xboxpro1/Switchless-Multi-ROM-for-THT-version/retroninja/applications/Switchless multi-ROM for CBM 1541/README.md

# Switchless multi-ROM for CBM 1541
Switches DOS ROM on the 1541 and other CBM IEC drives that uses 2364 ROMs. Can be used to switch ROM between CBM DOS/JiffyDOS/SpeedDOS/DolphinDOS and so on.

The switch is controlled by sending a command like *LOAD "2@RNROM",8* from the computer to switch to drive ROM image 2.

Read more in the User's guide.
