xboxpro1/Switchless-Multi-ROM-for-THT-version/retroninja/applications/Switchless multi-kernal for C64 longboard/firmware/README.md

# Firmware

The firmware directory contains source code along with some precompiled hex files for the microcontroller.

The source code is written using the Arduino environment and can be flashed directly from Arduino using an ISP programmer.
