xboxpro1/Switchless-Multi-ROM-for-THT-version/retroninja/applications/Switchless multi-ROM for CBM 1541/firmware/README.md

# Firmware

The firmware directory contains source code along with some precompiled hex files for the microcontroller.

The source code is written using the Arduino environment and can be flashed directly from Arduino using an ISP programmer.

Change log:  
1.0 - First public version for the old 1541 Multi-ROM board (rev 1, rev 1.1 & rev 2 boards) 14 May 2021  
1.1 - Updated sketch to suite the 2364 Multi-ROM board (rev 3 boards) 7 July 2022
