xboxpro1/Switchless-Multi-ROM-for-THT-version/applications/Application-Info.pdf

## CBM Switchless Multi ROM for 2364 & 27128 & 27256 ROMS

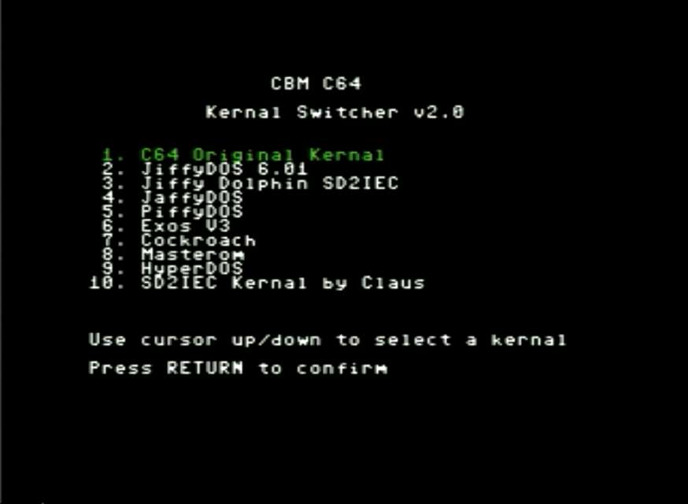
[picture p43: figure]

## Application Info

CBM Switchless Multi ROM for 2364 & 27128 & 27256 ROMS | Application Info ______________________________________________________________________

2

2

CBM Switchless Multi ROM for 2364 & 27128 & 27256 ROMS | Application Info ______________________________________________________________________

3

3

Table of Contents

CBM Switchless Multi ROM for 2364 & 27128 & 27256 ROMS | Application Info ______________________________________________________________________

4

4

Basics

Logic levels
Digital electronics rely on binary logic to store, process, and transmit data or information. Binary Logic refers to one of two states -- ON or OFF. This is commonly translated as a binary 1 or binary 0. A binary 1 is also referred to as a HIGH signal and a binary 0 is referred to as a LOW signal.
The strength of a signal is typically described by its voltage level.
How is a logic 0 (VIL) or a logic 1 (VIH) defined?
5V TTL Logic levels, maximum input LOW voltage (VIL) is 0.8 V, minimum input HIGH voltage (VIH) is 2 V.
AVR MCU Logic levels, maximum input LOW voltage (VIL) is 1.5 V,
minimum input HIGH voltage (VIH) is 3 V.
Active-Low and Active-High
When working with ICs and microcontrollers, you'll likely encounter pins that are active-low and pins that are active-high. Simply put, this just describes how the pin is activated. If it's an active-low pin, you must "pull" that pin LOW by connecting it to GND (ground). For an active high pin, you connect it to your HIGH voltage.
For example, let's say you have a flash-memory chip that has an output enable pin, OE. If you see the OE pin anywhere in the datasheet with a line over it like this, OE, then that pin is active-low. The OE pin would need to be pulled LOW in order to enable the output. If, however, the OE pin doesn't have a line over it, then it is active high, and it needs to be pulled HIGH in order to enable the output. Bit shift
A bit shift moves each digit in a number's binary representation left or right.
The left shift operator is written as "<<", the right shift operator is written as ">>". When shifting left, the most-significant bit is lost, and a 0 bit is inserted on the other end. When shifting right, the least-significant bit is lost and a 0 bit is inserted on the other end. A single left shift multiplies a number by 2, a single right shift divides a number by 2. Bit shift is faster than multiplying and dividing.
Example:
Binary | 0b0010 << 1 0b0100; 0b1010 >> 1 0b0101
Decimal | 2 << 1 4; | 10 >> 1 5

CBM Switchless Multi ROM for 2364 & 27128 & 27256 ROMS | Application Info ______________________________________________________________________

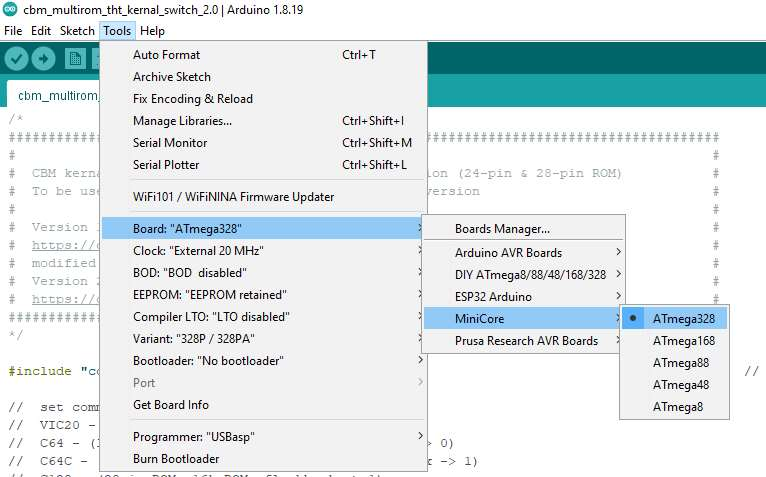
[picture p44: figure]

5

5

AVR MCU Firmware

Arduino IDE
Requirements can be found in the General-Info.pdf.
If you are new to Arduino programming, please see at: https://docs.arduino.cc/learn/starting-guide/getting-started-arduino
Please open the Arduino sketch from the /applications/arduino/firmware/v2.0/source folder with the Arduino IDE.
Then please adjust the AVR MCU you use.
Tools Board MiniCore AVR MCU (depends on what you use)

Necessary settings:
Clock External 20 MHz or 16 MHz, depends on what you use. Compiler LTO LTO disabled.
Variant depends on what you use.
Bootloader No bootloader.
If you use ISP programming you still have to set up your Programmer. All other settings can remain default.

CBM Switchless Multi ROM for 2364 & 27128 & 27256 ROMS | Application Info ______________________________________________________________________

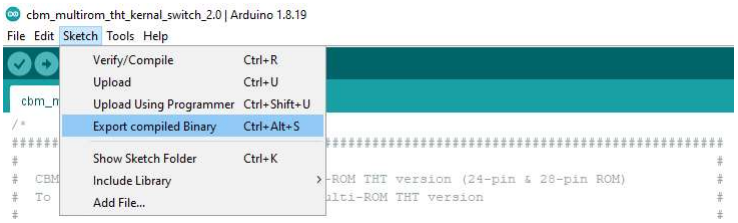
[picture p45: figure]

6

6

AVR MCU Firmware

Defining the Sketch
The sketch contains many comments and is self-explanatory. Please define the CBM Computer for which the firmware should be.

If you don't want the LED to blink, you can disable the LED by commenting it out.

These are all settings, nothing more needs to be done. Compiling
Now please compile the firmware and load it onto your MCU.
If you are programming via ISP, click Sketch Upload Using Programmer.
For an Universal Programmer or AVRDUDESS click Sketch Export compiled Binary.

CBM Switchless Multi ROM for 2364 & 27128 & 27256 ROMS | Application Info ______________________________________________________________________

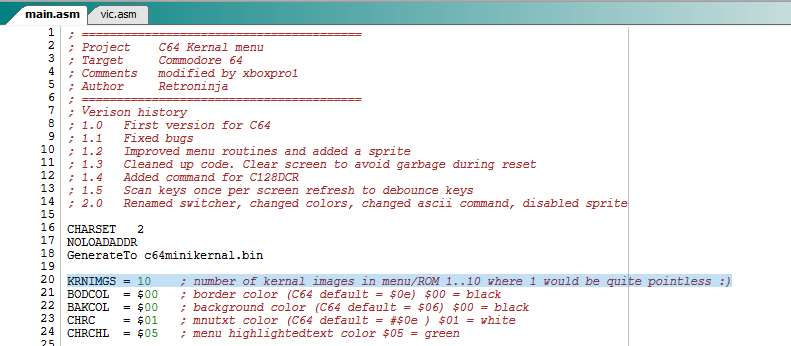
[picture p46: figure]
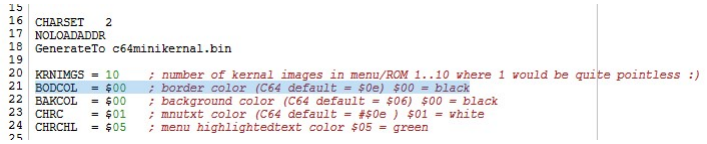
[picture p47: figure]

7

7

Mini Kernal

CBM prg Studio
Requirements can be found in the General-Info.pdf.
CBM prg Studio tutorials can be found here: https://oldskoolcoder.co.uk/cbm-prg-studio-tutorials/
Each CBM Computer has its own mini Kernal source file.
Folder /applications/cbm-prog-studio/mini-kernal/v2.0/ | /source.
Please open the project file with the ending “.cbmprj” of the desired CBM Computer using the CBM prg Studio program.
Now you can design your personal Switchless mini Kernal menu in the main.asm file. Such as the number of Kernal ROM image entries in the Switchless mini Kernal menu.

Also the frame, background and text colors.

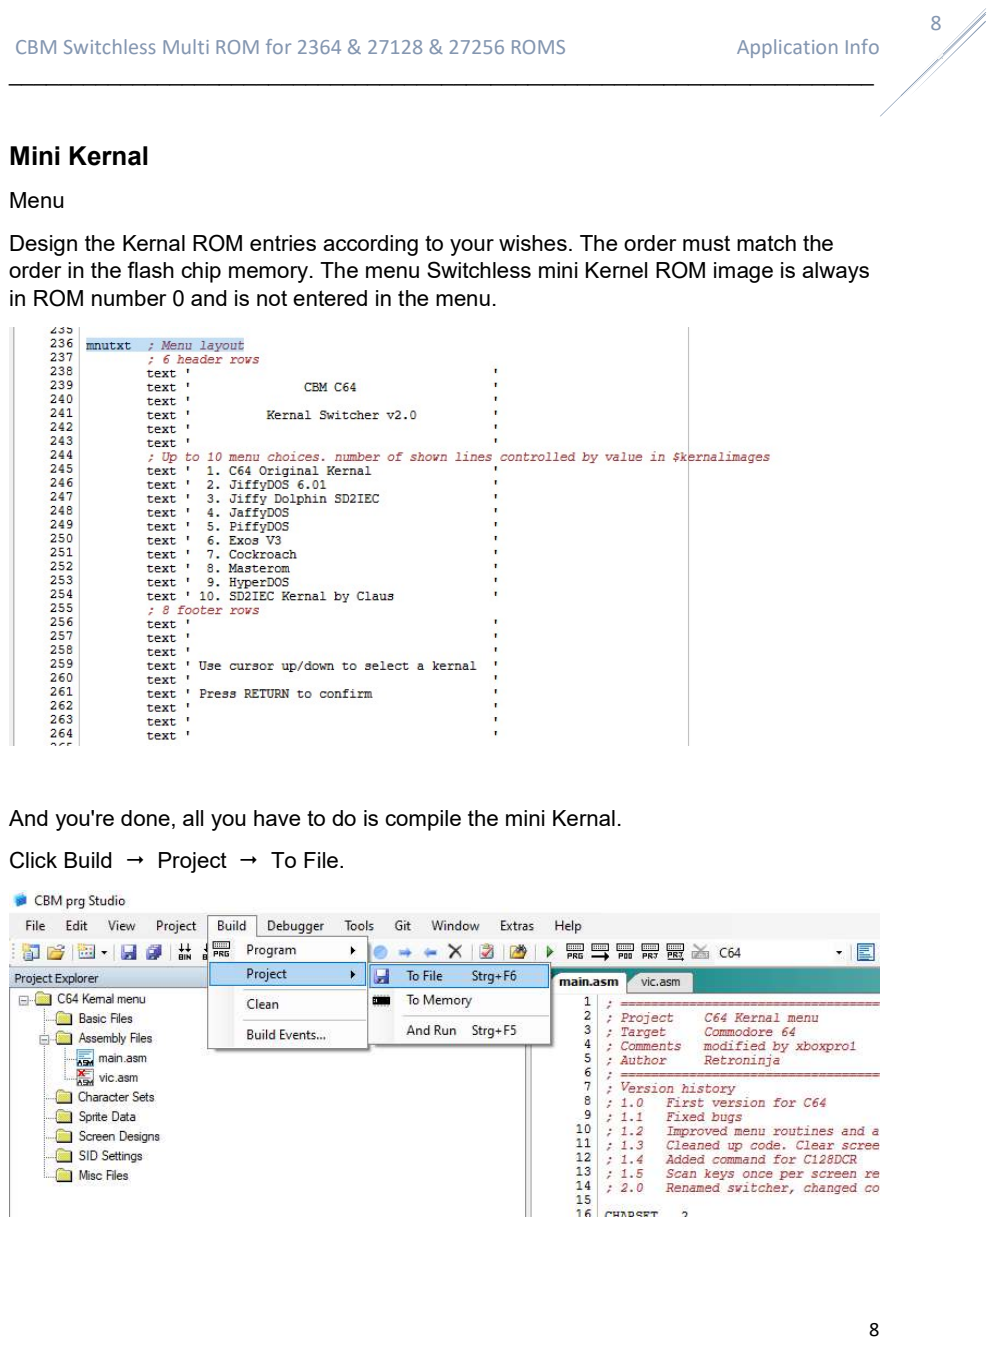
[picture p48: page 8]

CBM Switchless Multi ROM for 2364 & 27128 & 27256 ROMS | Application Info ______________________________________________________________________

8

8

Mini Kernal

Menu
Design the Kernal ROM entries according to your wishes. The order must match the order in the flash chip memory. The menu Switchless mini Kernel ROM image is always in ROM number 0 and is not entered in the menu.

And you're done, all you have to do is compile the mini Kernal. Click Build Project To File.

CBM Switchless Multi ROM for 2364 & 27128 & 27256 ROMS | Application Info ______________________________________________________________________

9

9

Flash-memory Chip

The Excel sheet in the tools folder, macros are harmless but not necessary, show you the memory allocation for the 8k, 16k and 32k ROM modes.
The mode depends on the CBM Mainboard / Kernal ROM chip.
VIC20 and C64 (longboard) normally has an 8k Kernal ROM.
C64C (shortboard) normally has an 16k Kernal ROM. Basic and Kernal in one ROM. C128 has two 16k ROM chips, one for the C128 mode and one for the C64C mode. C128DCR has a 32k Kernal ROM.
The memory area is divided into three banks. Bank 0 8k ROM, Bank 1 16k ROM and Bank 2 32k ROM. The memory banks are divided into ROM numbers for each Kernal. The Switchless mini Kernel ROM image is always in ROM number 0.
For Bank 1 and Bank 2, the kernel is selected in the firmware by bit shifting the ROM number to the left with the bank number.
Bank 0 VIC20, C64

Bank 1 C64C

Bank 1 C128

Bank 2 C128DCR

For more information, please see RetroNynjah's user guides in the retroninja folder.

Kernal | Mini Kernal 8k | CBM Kernal 8k | JiffyDOS 8k | JaffyDOS 8k | Exos V3 8k | HyperDOS 8k
Size | 8k | 8k | 8k | 8k | 8k | 8k
ROM number | 0 | 1 | 2 | 3 | 4 | 5
Kernal | C64 Basic 8k | Mini Kernal 8k | C64 Basic 8k | CBM Kernal 8k | C64 Basic 8k | JiffyDOS 8k
Size | 16k | | 16k | | 16k
ROM number | 0 | | 2 | | 4
Kernal | C128 Mini Kernal 16k | C128 CBM Kernal 16k | C128 JiffyDOS US 16k | C128 JiffyDOS DK 16k
Size | 16k | 16k | 16k | 16k
ROM number | 0 | 2 | 4 | 6
Kernal | C64 Basic 8k | C64 Mini-Kernal 8k | C128 Mini-Kernal 16k | C64 Basic 8k | C64 CBM-Kernal 8k | C128 CBM-Kernal 16k
Size | 32k | | | 32k
ROM number | 0 4

CBM Switchless Multi ROM for 2364 & 27128 & 27256 ROMS | Application Info ______________________________________________________________________

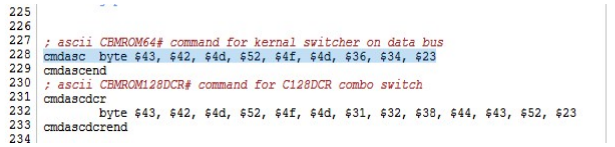
[picture p49: figure]
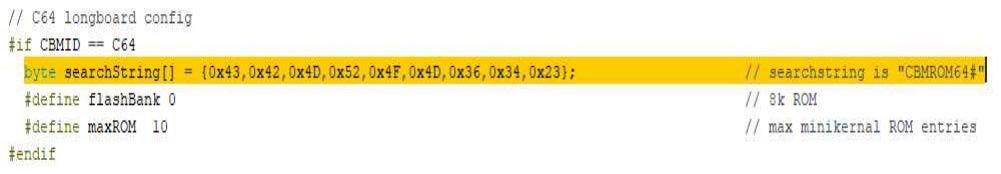
[picture p50: figure]

10

10

Change Source

You can of course change the source codes according to your requirements.
For example, changing the predefined command string of ”magic bytes”.
If you change the predefined command string in the Switchless mini Kernel source code, it also needs to be changed in the AVR MCU source code.

There are two PDF files in the tools folder with the ASCII and color codes. The codes are decimal and they must be converted to hexadecimal. Programming

Flash memory
To program the flash memory chip you need a USB universal programmer such as the TL866II Plus. A PLCC32-DIP32 adapter is also required.
Tutorial: https://projectiot123.com/2023/05/16/how-to-use-the-tl866ii-plus-programmer/ The easiest way is to first create a flash file with all the Kernal ROM images you want. Copy all the Kernal ROM images into a folder including a basic ROM.
For example, for an 8K ROM flash file, use the Windows command:
copy /b c64minikernal.bin+c64kernal.bin+jiffydos.bin+exos3.bin+sd2iec.bin flash.bin For example, for an 16K ROM flash file, use the Windows command:

copy /b basic.bin+minikernal.bin+basic.bin+c64kernal.bin+basic.bin+exos3.bin flash.bin For example, for an 32K ROM flash file, use the Windows command:
copy /b c64basic.bin+c64minikernal.bin+c128minikernal.bin+ c64basic.bin+c64kernal.bin+c128kernal.bin flash.bin

This is just an example, of course all of your desired Kernal images must be attached. Use the Universal programmer software to write the flash image to the flash chip.

CBM Switchless Multi ROM for 2364 & 27128 & 27256 ROMS | Application Info ______________________________________________________________________

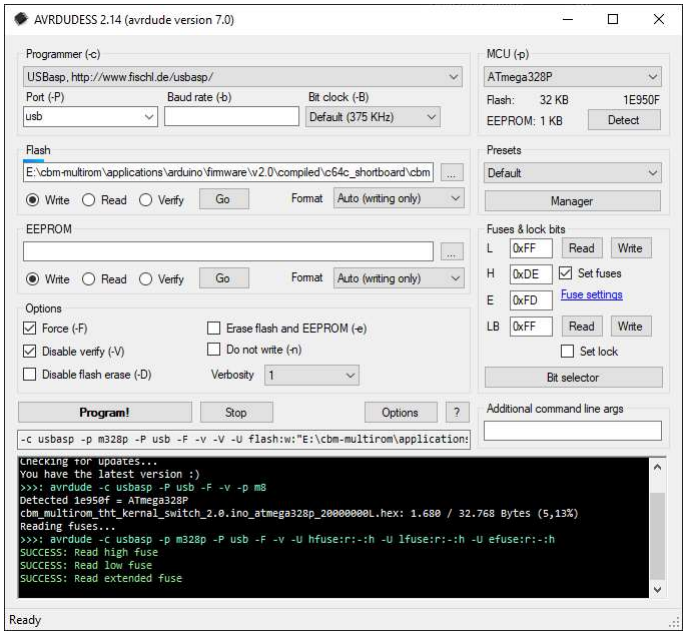
[picture p51: figure]

11

11

Programming

AVR MCU
You can also flash the AVR MCU with the USB universal programmer. Or you can use an ISP programmer to flash the MCU.
If you use an ISP programmer, I recommend the program AVRDUDESS. Requirements can be found in the General-Info.pdf.
With AVRDUDESS you can easily read and write the MCU fuses. There is also a fuse Bit selector and a link to a website where you can get the correct settings for the fuses.

Recommended fuse settings are in the fuses.txt file in the tools folder.

CBM Switchless Multi ROM for 2364 & 27128 & 27256 ROMS | Application Info ______________________________________________________________________

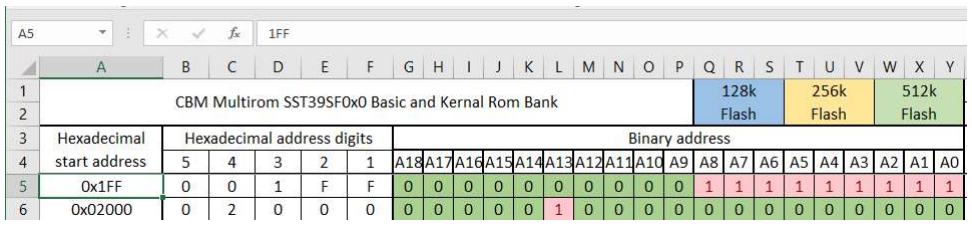
[picture p52: figure]

12

12

Tools

Excel sheet
In the Excel sheet addresscalc.xlsm in the tools folder you can enter any addresses from 0 to 7FFFF at cell A5.
Please do not write 0x at the beginning, Excel will do that itself.
This causes the address bits A0 to A18 to be set according to the respective address.

The Excel sheet has a sheet protection so that no formula can be deleted accidentally. The code to remove the sheet protection is 1234.
CircuitVerse
On CircuitVerse you can create simulations with digital components. https://circuitverse.org/simulator You can use the MultiromOE.cv file in the tools folder to simulate IC5 the single “AND”

Gate for experimental testing.
To use it click: Project Import file

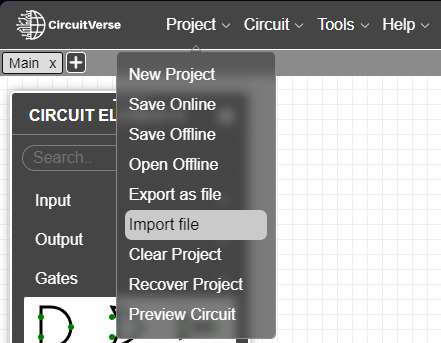
[picture p53: figure]
