xboxpro1/Switchless-Multi-ROM-for-THT-version/tools/cbm-color-codes.pdf

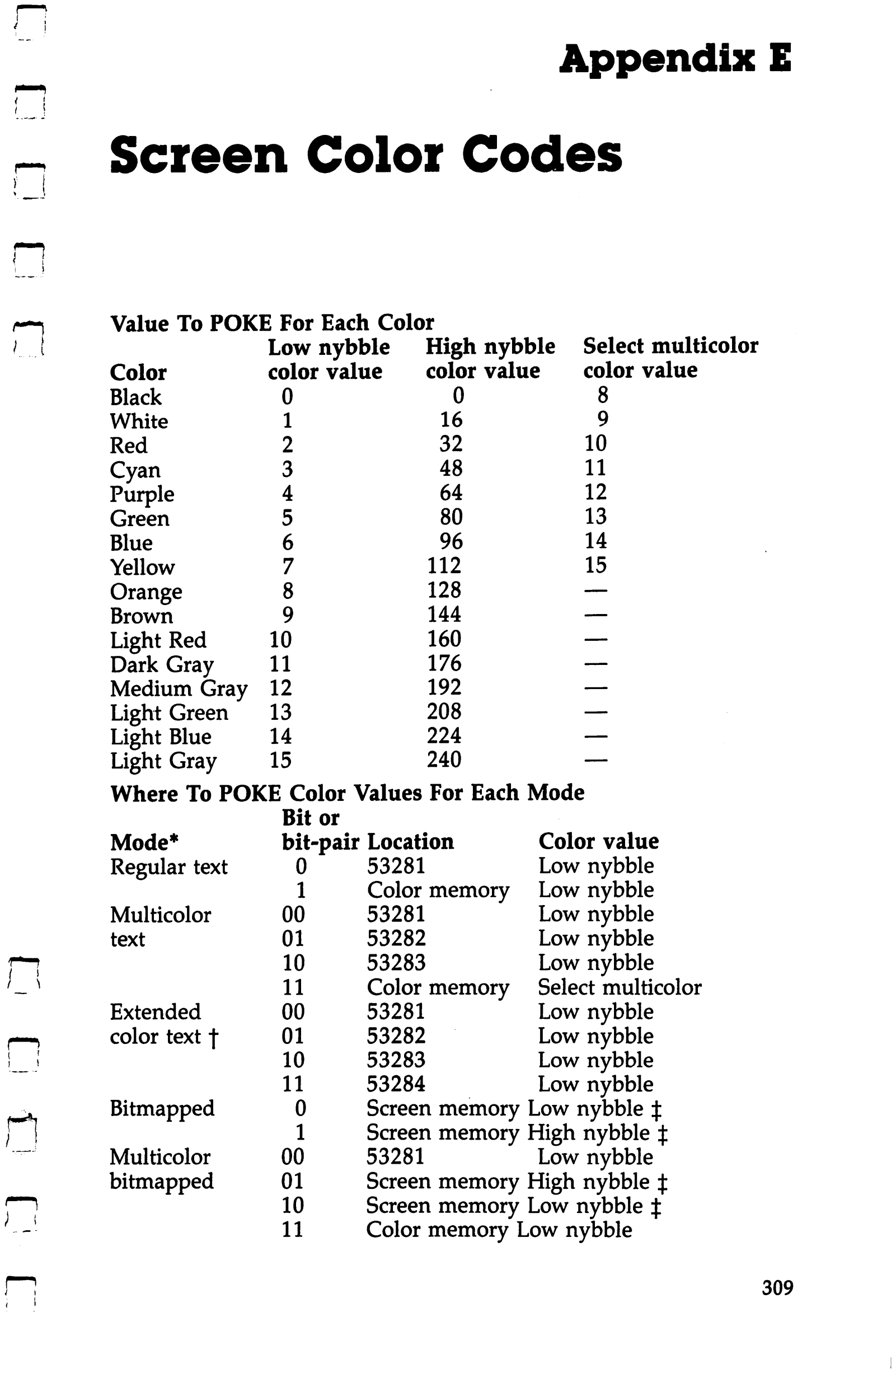
[picture p54: figure]
