xboxpro1/Switchless-Multi-ROM-for-THT-version/images/cbm-multirom-back-transparent.png

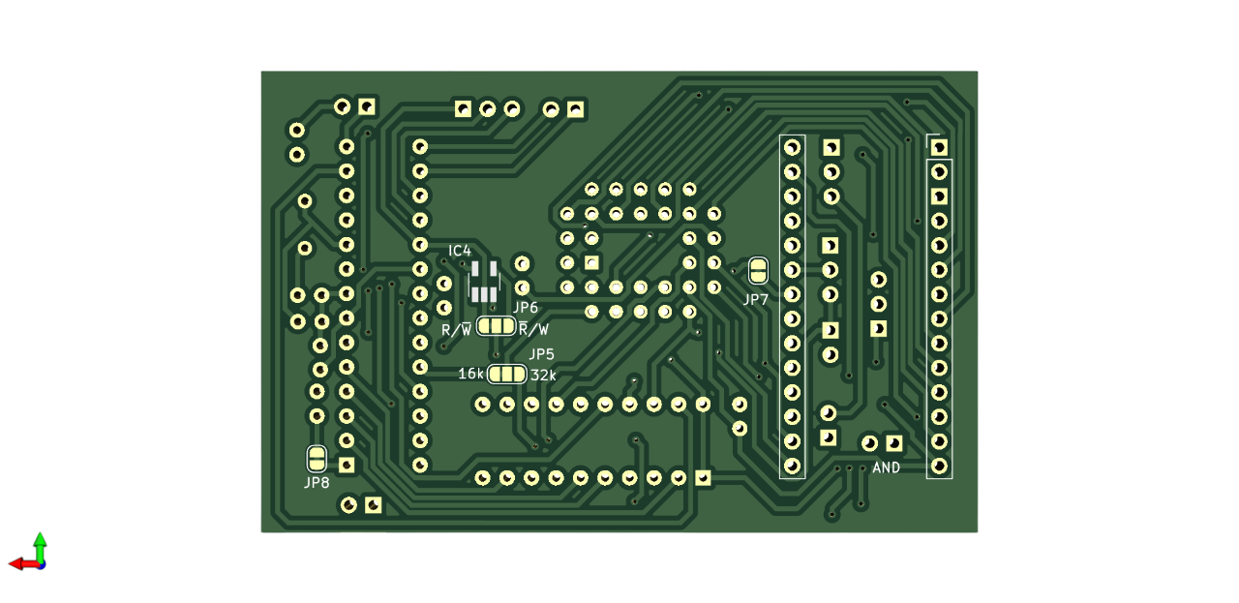
images/cbm-multirom-back-transparent.png
