xboxpro1/Switchless-Multi-ROM-for-THT-version/images/cbm-multirom-front-transparent.png

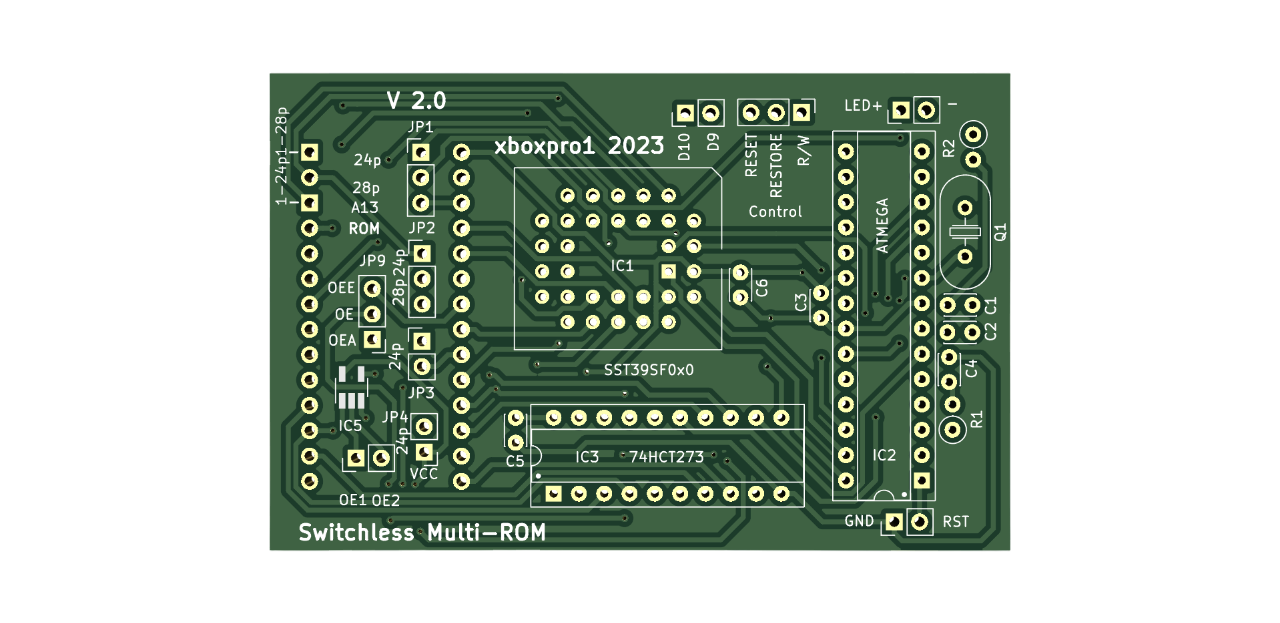
images/cbm-multirom-front-transparent.png
