xboxpro1/Switchless-Multi-ROM-for-THT-version/images/cbm-multirom-smd-pcb-front.png

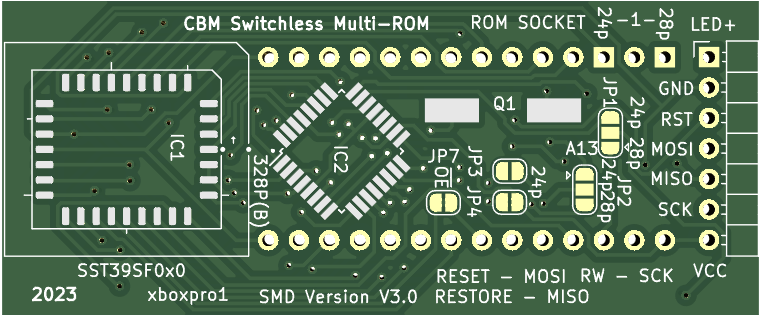
images/cbm-multirom-smd-pcb-front.png
