xboxpro1/Switchless-Multi-ROM-for-THT-version/pictures/keyboard-holder.jpg

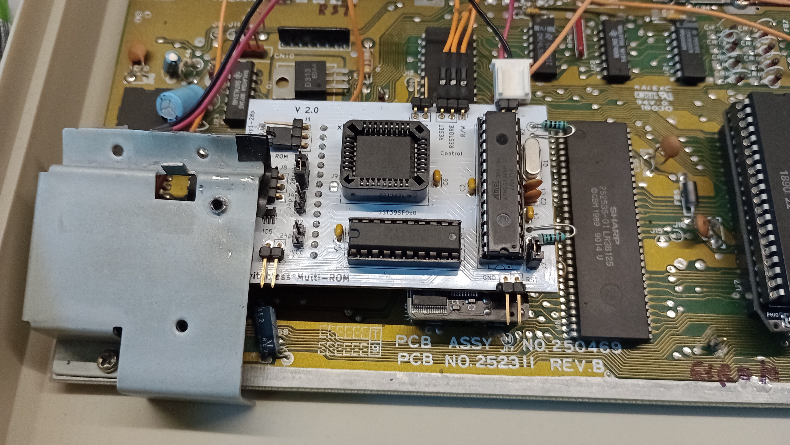
pictures/keyboard-holder.jpg
