xboxpro1/Switchless-Multi-ROM-for-THT-version/tools/plcc32-adapter.jpg

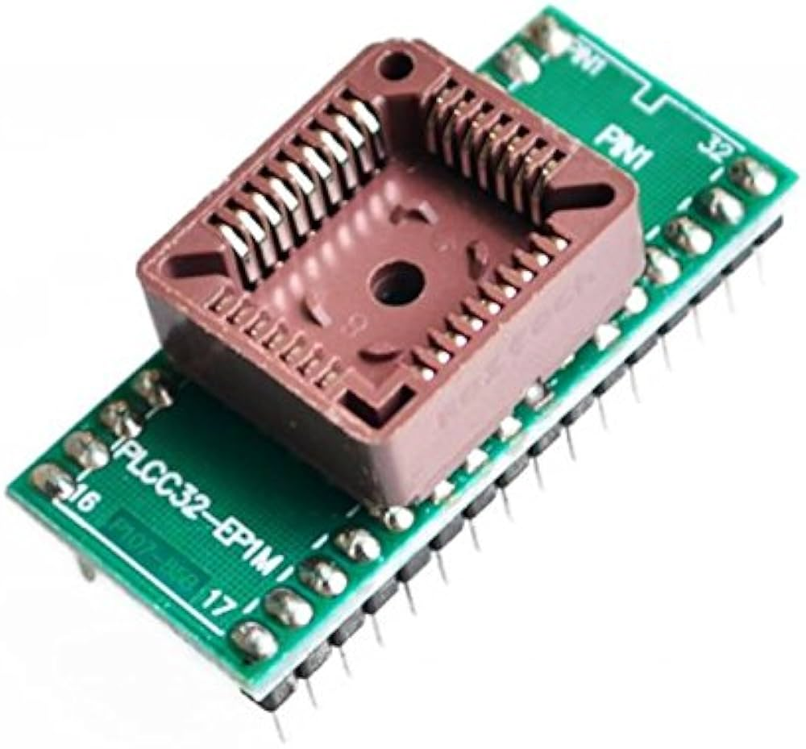
tools/plcc32-adapter.jpg
