xboxpro1/Switchless-Multi-ROM-for-THT-version/tools/tl866ii.jpg

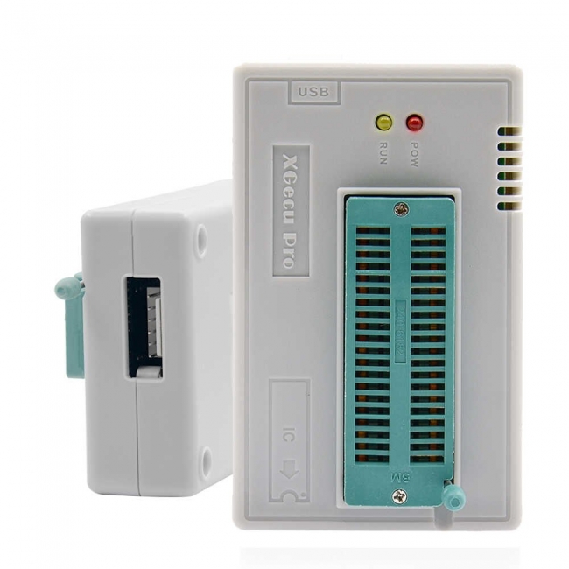
tools/tl866ii.jpg
