xboxpro1/Switchless-Multi-ROM-for-THT-version/pictures/pcb-assembled.jpg

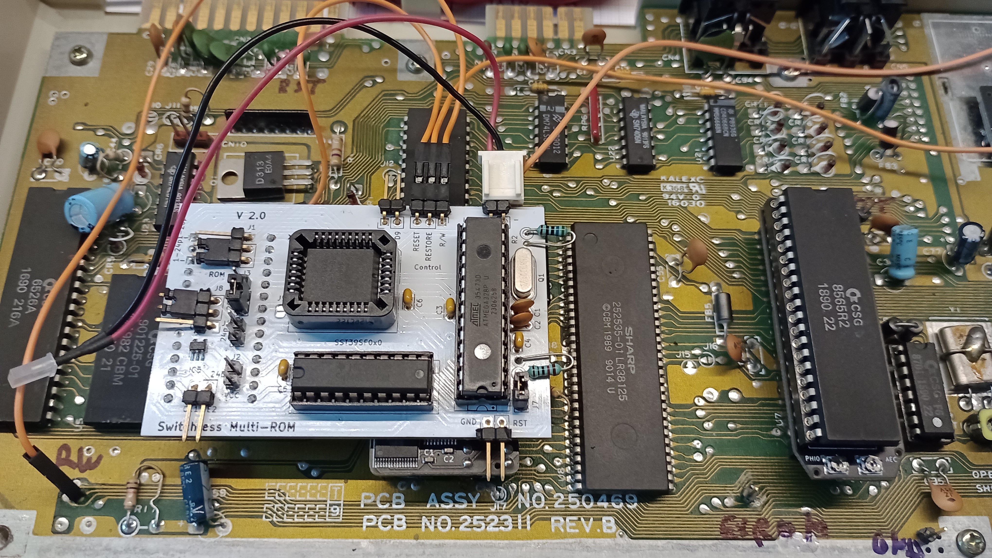
pictures/pcb-assembled.jpg
