xboxpro1/Switchless-Multi-ROM-for-THT-version/hardware/V2.0/cbm-multirom-shematic.pdf

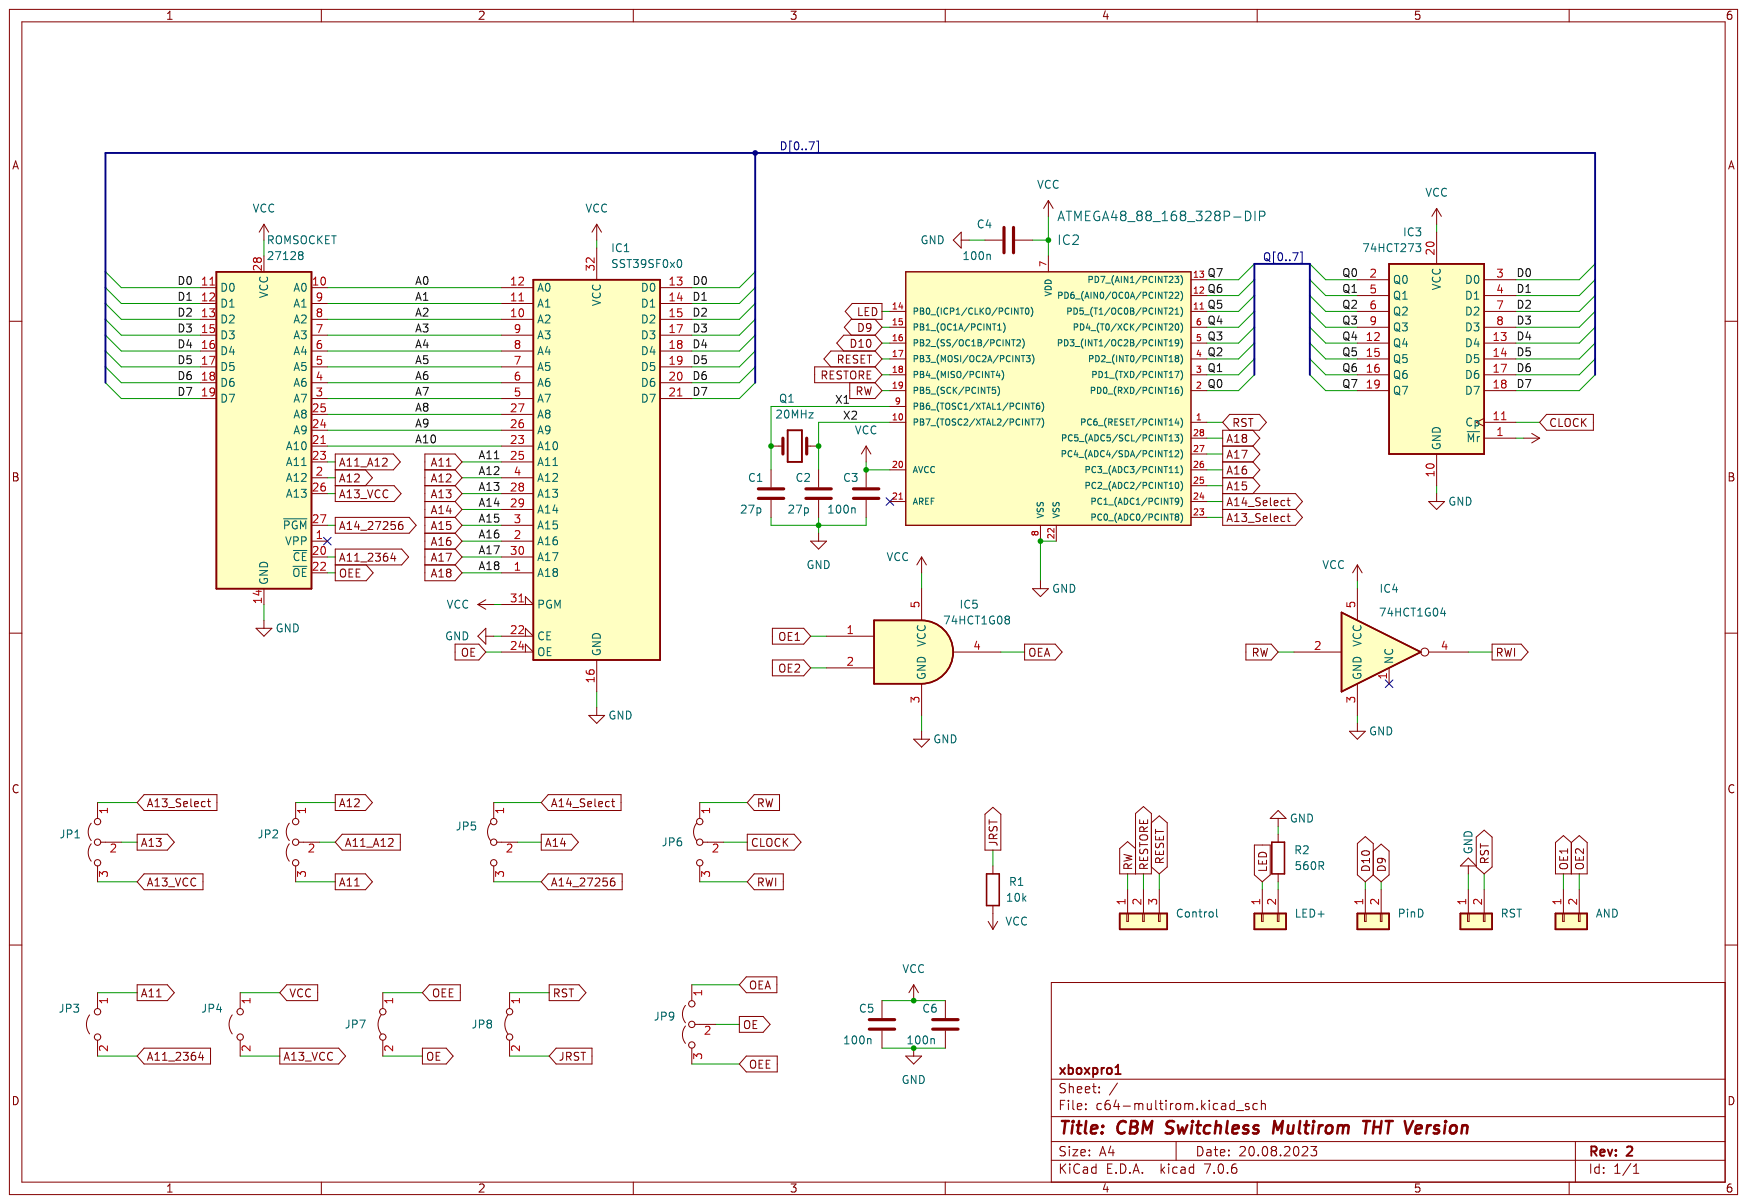
[picture p106: page 1]
